slimcdk/google-pixel-tablet/electronics/electronics.kicad_sch

## KiCad design electronics/electronics.kicad_sch (2023-11-19)

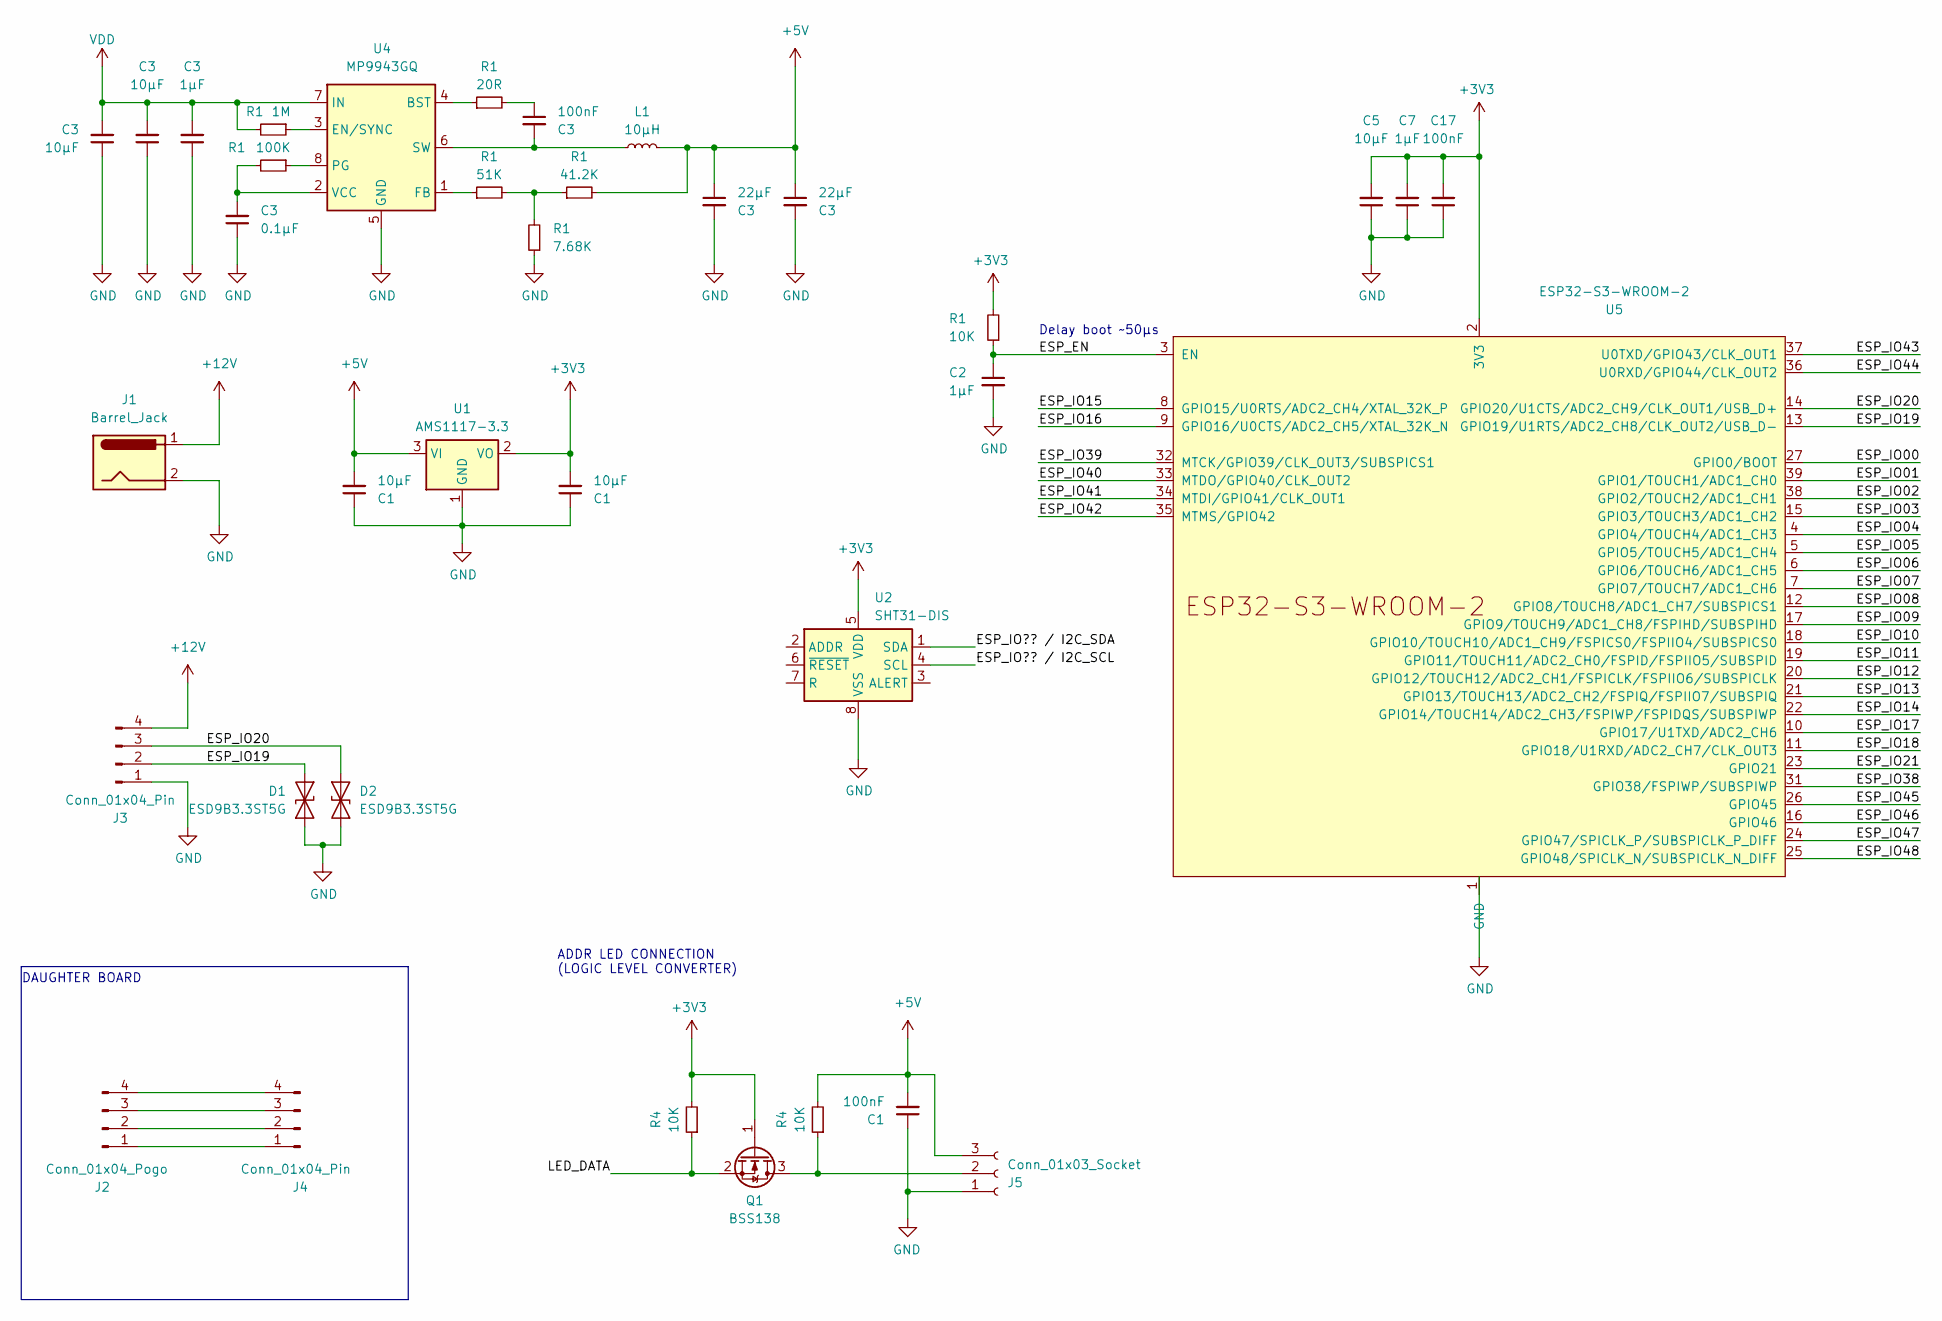
[picture p15: schematic electronics.kicad_sch]

Parts:
C1, C17: 100nF; C_0402_1005Metric
C2, C7: 1µF; C_0402_1005Metric
C3: 100nF; C_0402_1005Metric; Voltage 35V
C5: 10µF; C_0402_1005Metric
D1, D2: ESD9B3.3ST5G; D_SOD-923
J1: Barrel_Jack
J2: Conn_01x04_Pogo
J3, J4: Conn_01x04_Pin
J5: Conn_01x03_Socket
L1: 10µH
Q1: BSS138; SOT-23
R1: 1M; R_0805_2012Metric_Pad1.20x1.40mm_HandSolder
R4: 10K; R_0805_2012Metric_Pad1.20x1.40mm_HandSolder
U1: AMS1117-3.3; SOT-223-3_TabPin2
U2: SHT31-DIS; Sensirion_DFN-8-1EP_2.5x2.5mm_P0.5mm_EP1.1x1.7mm
U4: MP9943GQ; DFN-8-1EP_3x3mm_P0.65mm_EP1.7x2.05mm
U5: ESP32-S3-WROOM-2

Connections:
+3V3: C1.2, C5.2, C7.2, C17.2, Q1.1 (G), R1.2, R4.2, U1.2 (VO), U2.5 (VDD), U5.2 (3V3)
+5V: C1.2, C3.1, J5.3, L1.2, R1.2, R4.2, U1.3 (VI)
+12V: J1.1, J3.4
ESP_EN: C2.1, R1.1, U5.3 (EN)
ESP_IO00: U5.27 (GPIO0/BOOT)
ESP_IO01: U5.39 (GPIO1/TOUCH1/ADC1_CH0)
ESP_IO02: U5.38 (GPIO2/TOUCH2/ADC1_CH1)
ESP_IO03: U5.15 (GPIO3/TOUCH3/ADC1_CH2)
ESP_IO04: U5.4 (GPIO4/TOUCH4/ADC1_CH3)
ESP_IO05: U5.5 (GPIO5/TOUCH5/ADC1_CH4)
ESP_IO06: U5.6 (GPIO6/TOUCH6/ADC1_CH5)
ESP_IO07: U5.7 (GPIO7/TOUCH7/ADC1_CH6)
ESP_IO08: U5.12 (GPIO8/TOUCH8/ADC1_CH7/SUBSPICS1)
ESP_IO09: U5.17 (GPIO9/TOUCH9/ADC1_CH8/FSPIHD/SUBSPIHD)
ESP_IO10: U5.18 (GPIO10/TOUCH10/ADC1_CH9/FSPICS0/FSPIIO4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)
ESP_IO11: U5.19 (GPIO11/TOUCH11/ADC2_CH0/FSPID/FSPIIO5/S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)
ESP_IO12: U5.20 (GPIO12/TOUCH12/ADC2_CH1/FSPICLK/FSPIIO6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)
ESP_IO13: U5.21 (GPIO13/TOUCH13/ADC2_CH2/FSPIQ/FSPIIO7/S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)
ESP_IO14: U5.22 (GPIO14/TOUCH14/ADC2_CH3/FSPIWP/FSPIDQS/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)
ESP_IO15: U5.8 (GPIO15/U0RTS/ADC2_CH4/XTAL_32K_P)
ESP_IO16: U5.9 (GPIO16/U0CTS/ADC2_CH5/XTAL_32K_N)
ESP_IO17: U5.10 (GPIO17/U1TXD/ADC2_CH6)
ESP_IO18: U5.11 (GPIO18/U1RXD/ADC2_CH7/CLK_OUT3)
ESP_IO19: D1.1 (A1), J3.2, U5.13 (GPIO19/U1RTS/ADC2_CH8/CLK_OUT2/USB_D-)
ESP_IO20: D2.1 (A1), J3.3, U5.14 (GPIO20/U1CTS/ADC2_CH9/CLK_OUT1/USB_D+)
ESP_IO21: U5.23 (GPIO21)
ESP_IO38: U5.31 (GPIO38/FSPIWP/SUBSPIWP)
ESP_IO39: U5.32 (MTCK/GPIO39/CLK_OUT3/SUBSPICS1)
ESP_IO40: U5.33 (MTDO/GPIO40/CLK_OUT2)
ESP_IO41: U5.34 (MTDI/GPIO41/CLK_OUT1)
ESP_IO42: U5.35 (MTMS/GPIO42)
ESP_IO43: U5.37 (U0TXD/GPIO43/CLK_OUT1)
ESP_IO44: U5.36 (U0RXD/GPIO44/CLK_OUT2)
ESP_IO45: U5.26 (GPIO45)
ESP_IO46: U5.16 (GPIO46)
ESP_IO47: U5.24 (GPIO47/SPICLK_P/SUBSPICLK_P_DIFF)
ESP_IO48: U5.25 (GPIO48/SPICLK_N/SUBSPICLK_N_DIFF)
ESP_IO?? / I2C_SCL: U2.4 (SCL)
ESP_IO?? / I2C_SDA: U2.1 (SDA)
GND: C1.1, C2.2, C3.1, C3.2, C5.1, C7.1, C17.1, D1.2 (A2), D2.2 (A2), J1.2, J3.1, J5.1, R1.1, U1.1 (GND), U2.8 (VSS), U2.9 (VSS), U4.5 (GND), U5.1 (GND), U5.40 (GND), U5.41 (GND)
LED_DATA: Q1.2 (S), R4.1
unnamed: C3.1, R1.2
unnamed: C3.2, L1.1, R1.2, U4.2 (VCC), U4.6 (SW)
unnamed: J2.1, J4.1
unnamed: J2.2, J4.2
unnamed: J2.3, J4.3
unnamed: J2.4, J4.4
unnamed: J5.2, Q1.3 (D), R4.1
unnamed: R1.1, R1.2, U4.1 (FB), U4.3 (EN/SYNC), U4.4 (BST), U4.8 (PG)
VDD: C3.2, R1.2, U4.7 (IN)

Notes on the sheet:
DAUGHTER BOARD
ADDR LED CONNECTION (LOGIC LEVEL CONVERTER)
Delay boot ~50µs
